vihaangkanodia632-lang/Smart-Tool-Management-System-/Images/IMG_20260607_231803.jpg

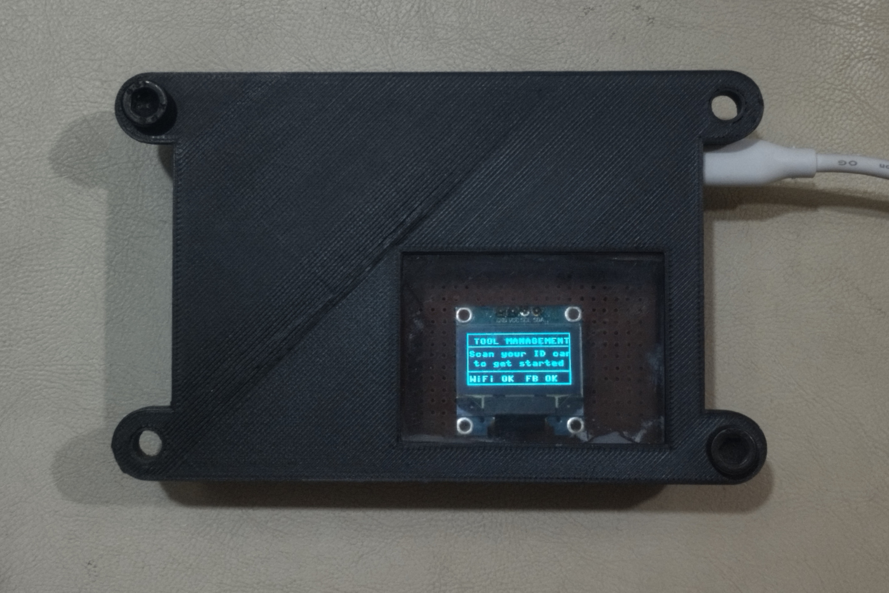
Images/IMG_20260607_231803.jpg
